skiselev/ParPortProp/KiCad/PPP.sch

## KiCad design KiCad/PPP.sch (2026-01-06)

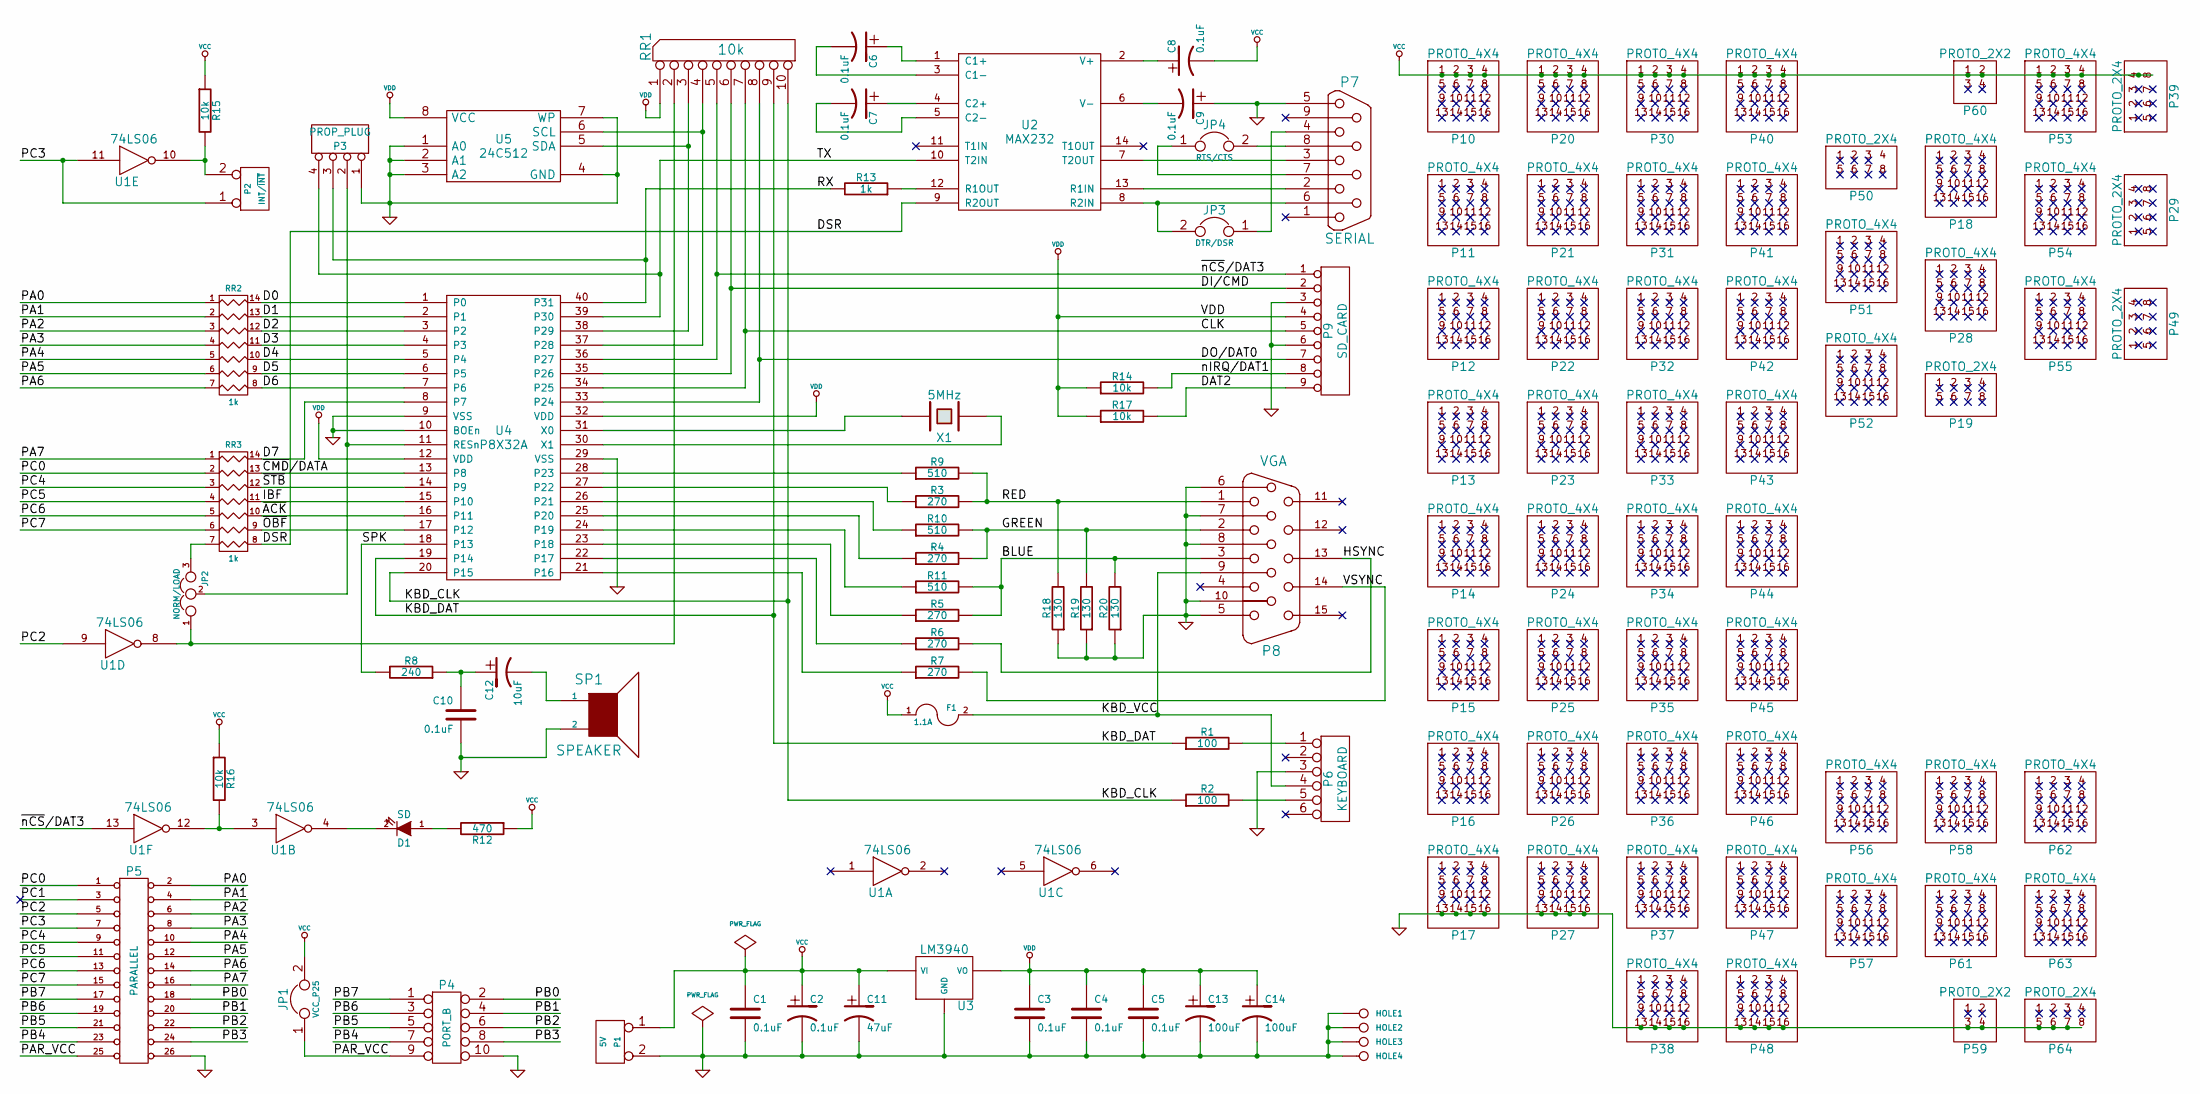
[picture p16: schematic PPP.sch]

Parts:
C1, C2, C3, C4, C5, C6, C7, C8, C9, C10: 0.1uF
C11: 47uF
C12: 10uF
C13, C14: 100uF
D1: SD
F1: 1.1A
HOLE1, HOLE2, HOLE3, HOLE4: CONN_1
JP1: VCC_P25
JP2: NORM/LOAD
JP3: DTR/DSR
JP4: RTS/CTS
P1: 5V
P2: INT/~INT
P3: PROP_PLUG
P4: PORT_B
P5: PARALLEL
P6: KEYBOARD
P7: SERIAL
P8: VGA
P9: SD_CARD
P10, P11, P12, P13, P14, P15, P16, P17, P18, P20, P21, P22, P23, P24, P25, P26, P27, P28, P30, P31, P32, P33, P34, P35, P36, P37, P38, P40, P41, P42, P43, P44, P45, P46, P47, P48, P51, P52, P53, P54, P55, P56, P57, P58, P61, P62, P63: PROTO_4X4
P19, P29, P39, P49, P50, P64: PROTO_2X4
P59, P60: PROTO_2X2
R1, R2: 100
R3, R4, R5, R6, R7: 270
R8: 240
R9, R10, R11: 510
R12: 470
R13: 1k
R14, R15, R16, R17: 10k
R18, R19, R20: 130
RR1: 10k
RR2, RR3: 1k
SP1: SPEAKER
U1: 74LS06
U2: MAX232
U3: LM3940
U4: P8X32A
U5: 24C512
X1: 5MHz

Connections:
BLUE: P8.3, R5.2, R11.2, R20.2
CLK: P9.5, RR1.7, U4.34 (P25)
D0: RR2.14 (R3), U4.1 (P0)
D1: RR2.13 (R4), U4.2 (P1)
D2: RR2.12 (R5), U4.3 (P2)
D3: RR2.11 (R6), U4.4 (P3)
D4: RR2.10 (R7), U4.5 (P4)
D5: RR2.9 (R8), U4.6 (P5)
D6: RR2.8, U4.7 (P6)
D7: RR3.14 (R3), U4.8 (P7)
DAT2: P9.9, R17.2
DI/CMD: P9.2, RR1.6, U4.35 (P26)
DO/DAT0: P9.7, RR1.8, U4.33 (P24)
DSR: RR3.8, U2.9 (R2OUT)
GND: C1.2, C2.2, C3.2, C4.2, C5.2, C9.1, C10.2, C11.2, C13.2, C14.2, HOLE1.1, HOLE2.1, HOLE3.1, HOLE4.1, P1.2 (PM), P3.1, P4.10, P5.26 (P22), P6.3, P7.5, P8.5, P8.6, P8.7, P8.8, P8.10, P9.3, P9.6, P17.13, P17.14, P17.15, P17.16, P27.13, P27.14, P27.15, P27.16, P38.13, P38.14, P38.15, P38.16, P48.13, P48.14, P48.15, P48.16, P59.3, P59.4, P64.5, P64.6, P64.7, P64.8, R18.1, R19.1, R20.1, SP1.2, U3.GND, U4.9 (VSS), U4.10 (BOEn), U4.29 (VSS), U5.1 (A0), U5.2 (A1), U5.3 (A2), U5.4 (GND), U5.7 (WP)
GREEN: P8.2, R4.2, R10.2, R19.2
HSYNC: P8.13, R6.2
IBF: RR3.11 (R6), U4.15 (P10)
KBD_CLK: R2.1, RR1.10, U4.20 (P15)
KBD_DAT: R1.1, RR1.9, U4.19 (P14)
KBD_VCC: F1.2, P6.4, P8.9
unnamed: C6.1, U2.1 (C1+)
unnamed: C6.2, U2.3 (C1-)
unnamed: C7.1, U2.4 (C2+)
unnamed: C7.2, U2.5 (C2-)
unnamed: C8.1, U2.2 (V+)
unnamed: C9.2, U2.6 (V-)
unnamed: C10.1, C12.1, R8.1
unnamed: C12.2, SP1.1
unnamed: D1.1 (A), R12.2
unnamed: D1.2 (K), U1.4
unnamed: JP2.1, RR1.2, U1.8
unnamed: JP2.2, P3.2, U4.11 (RESn)
unnamed: JP2.3, RR3.7
unnamed: JP3.1, P7.4
unnamed: JP3.2, P7.6, U2.8 (R2IN)
unnamed: JP4.1, P7.7
unnamed: JP4.2, P7.8
unnamed: P2.2 (PM), R15.2, U1.10
unnamed: P6.1, R1.2
unnamed: P6.5, R2.2
unnamed: P7.2, U2.13 (R1IN)
unnamed: P7.3, U2.7 (T2OUT)
unnamed: R3.1, U4.27 (P22)
unnamed: R4.1, U4.25 (P20)
unnamed: R5.1, U4.23 (P18)
unnamed: R6.1, U4.22 (P17)
unnamed: R7.1, U4.21 (P16)
unnamed: R9.1, U4.28 (P23)
unnamed: R10.1, U4.26 (P21)
unnamed: R11.1, U4.24 (P19)
unnamed: R13.1, U2.12 (R1OUT)
unnamed: R16.2, U1.3, U1.12
unnamed: RR1.3, U4.38 (P29), U5.5 (SDA)
unnamed: RR1.4, U4.37 (P28), U5.6 (SCL)
unnamed: U4.30 (X1), X1.1
unnamed: U4.31 (X0), X1.2
PA0: P5.2, RR2.1
PA1: P5.4, RR2.2
PA2: P5.6, RR2.3
PA3: P5.8, RR2.4
PA4: P5.10, RR2.5
PA5: P5.12, RR2.6
PA6: P5.14, RR2.7
PA7: P5.16, RR3.1
PAR_VCC: JP1.1, P4.9, P5.25 (P24)
PB0: P4.2, P5.18
PB1: P4.4, P5.20
PB2: P4.6, P5.22
PB3: P4.8, P5.24 (P20)
PB4: P4.7, P5.23
PB5: P4.5, P5.21
PB6: P4.3, P5.19
PB7: P4.1, P5.17
PC0: P5.1, RR3.2
PC1: P5.3
PC2: P5.5, U1.9
PC3: P2.1, P5.7, U1.11
PC4: P5.9, RR3.3
PC5: P5.11, RR3.4
PC6: P5.13, RR3.5
PC7: P5.15, RR3.6
RED: P8.1, R3.2, R9.2, R18.2
RX: P3.3, R13.2, U4.40 (P31)
SPK: R8.2, U4.18 (P13)
TX: P3.4, U2.10 (T2IN), U4.39 (P30)
VCC: C1.1, C2.1, C8.2, C11.1, F1.1, JP1.2, P1.1, P10.1, P10.2, P10.3, P10.4, P20.1, P20.2, P20.3, P20.4, P30.1, P30.2, P30.3, P30.4, P39.4, P39.8, P40.1, P40.2, P40.3, P40.4, P53.1, P53.2, P53.3, P53.4, P60.1, P60.2, R12.1, R15.1, R16.1, U3.VI
VDD: C3.1, C4.1, C5.1, C13.1, C14.1, P9.4, R14.1, R17.1, RR1.1 (COM), U3.VO, U4.12 (VDD), U4.32 (VDD), U5.8 (VCC)
VSYNC: P8.14, R7.2
nIRQ/DAT1: P9.8, R14.2
~ACK: RR3.10 (R7), U4.16 (P11)
~CMD~/DATA: RR3.13 (R4), U4.13 (P8)
~OBF: RR3.9 (R8), U4.17 (P12)
~STB: RR3.12 (R5), U4.14 (P9)
~nCS~/DAT3: P9.1, RR1.5, U1.13, U4.36 (P27)
